atomsfat/arduino-timer/ProgramarCmd.h

/* 
 * File:   ProgamarCmd.h
 * Author: atoms
 *
 * Created on Agosto 11, 2013, 1:35 PM
 */

#ifndef _PROGRAMARCMD_H
#define	_PROGRAMARCMD_H
#include "Command.h"


class ProgramarCmd : public Command {
private:
    bool procesa;
    bool procesaHoraInicio;
    bool procesaTiempo;
    bool procesaDia;
 //   bool procesaDiaComplete;


    uint8_t hourPG1;
    uint8_t minutePG1;
    uint8_t minutesOnPG1;
    uint8_t dayPG1;

    int dayWeek;

    int currentDay;

public:
    ProgramarCmd(Model* model,  Controller* controller);
  
    virtual ~ProgramarCmd();

    void ok();
    void cancel();
    void up() ;
    void down();
    void display( char msg[]);



};

#endif	/* _PROGRAMARCMD_H */
